Jeff-Birt/Casio_12Pin/simple_con_pcb.sch

## EAGLE design simple_con_pcb.sch (2022-04-04)

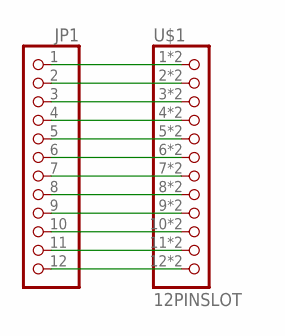
[picture p5: schematic simple_con_pcb.sch]

Parts:
JP1: PINHD-1X12; 1X12
U$1: 12PINSLOT; 1X12_SLOT

Connections:
unnamed: JP1.1, U$1.1
unnamed: JP1.2, U$1.2
unnamed: JP1.3, U$1.3
unnamed: JP1.4, U$1.4
unnamed: JP1.5, U$1.5
unnamed: JP1.6, U$1.6
unnamed: JP1.7, U$1.7
unnamed: JP1.8, U$1.8
unnamed: JP1.9, U$1.9
unnamed: JP1.10, U$1.10
unnamed: JP1.11, U$1.11
unnamed: JP1.12, U$1.12
